paula-delrio-arteaga/FABACADEMY-1/Images/Lasercut.png

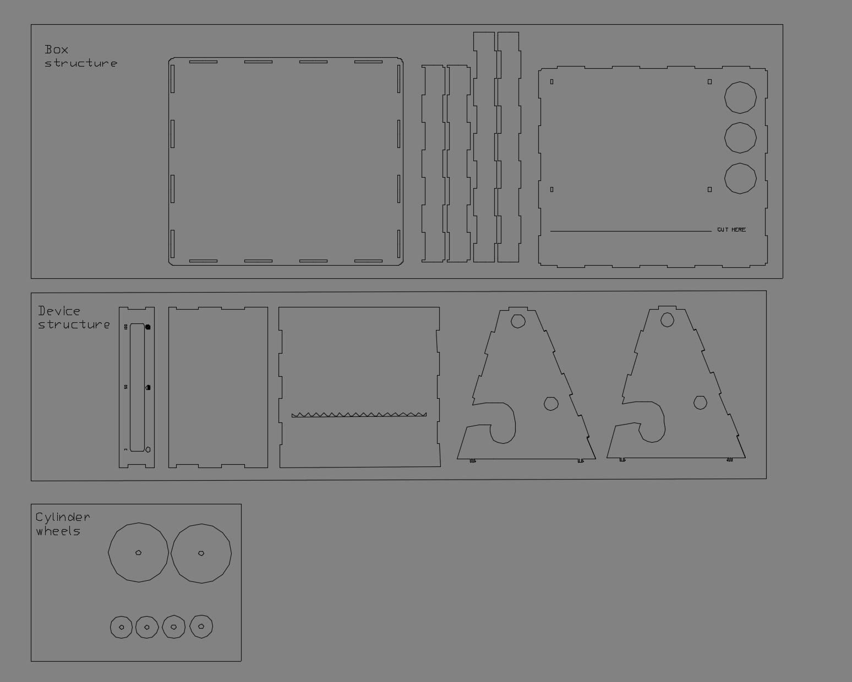
Images/Lasercut.png
