paula-delrio-arteaga/FABACADEMY-1/Images/prototyping_1.jpg

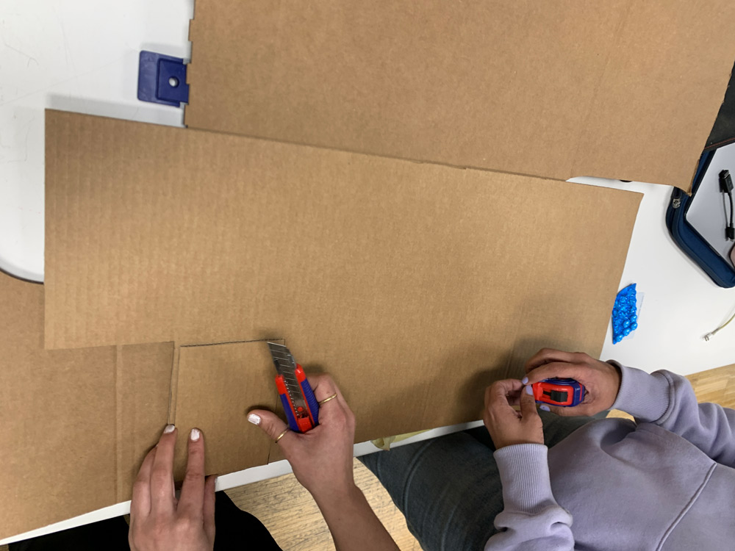
Images/prototyping_1.jpg
