paula-delrio-arteaga/FABACADEMY-1/Images/prototyping_2.jpg

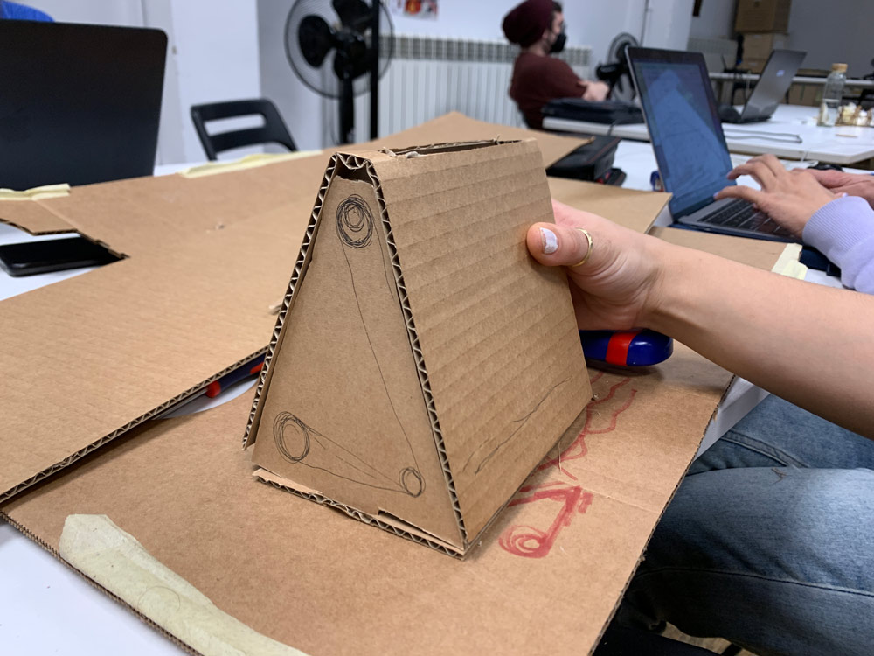
Images/prototyping_2.jpg
