paula-delrio-arteaga/FABACADEMY-1/Images/prototyping_3.jpg

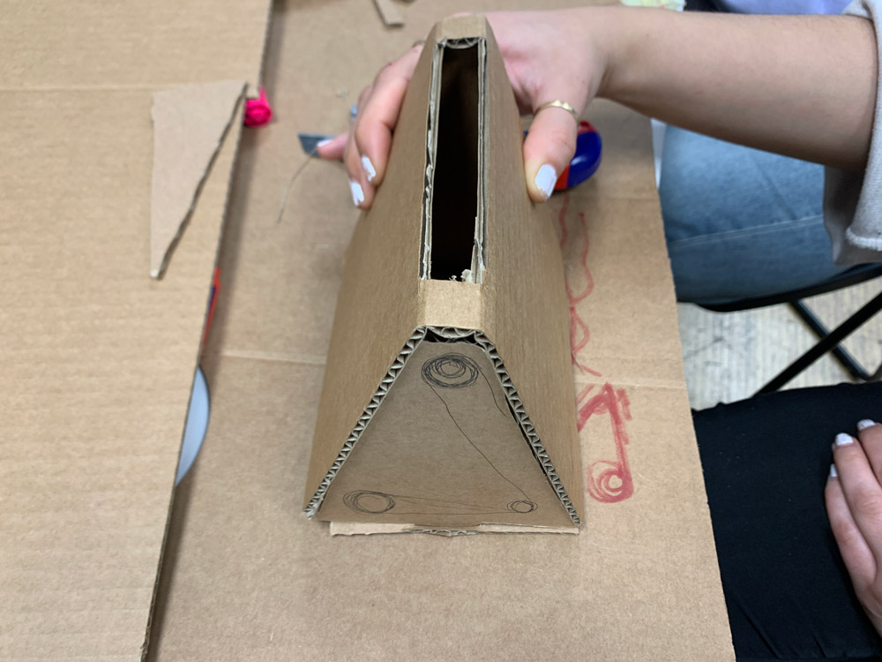
Images/prototyping_3.jpg
