paula-delrio-arteaga/FABACADEMY-1/Images/reference_01.jpg

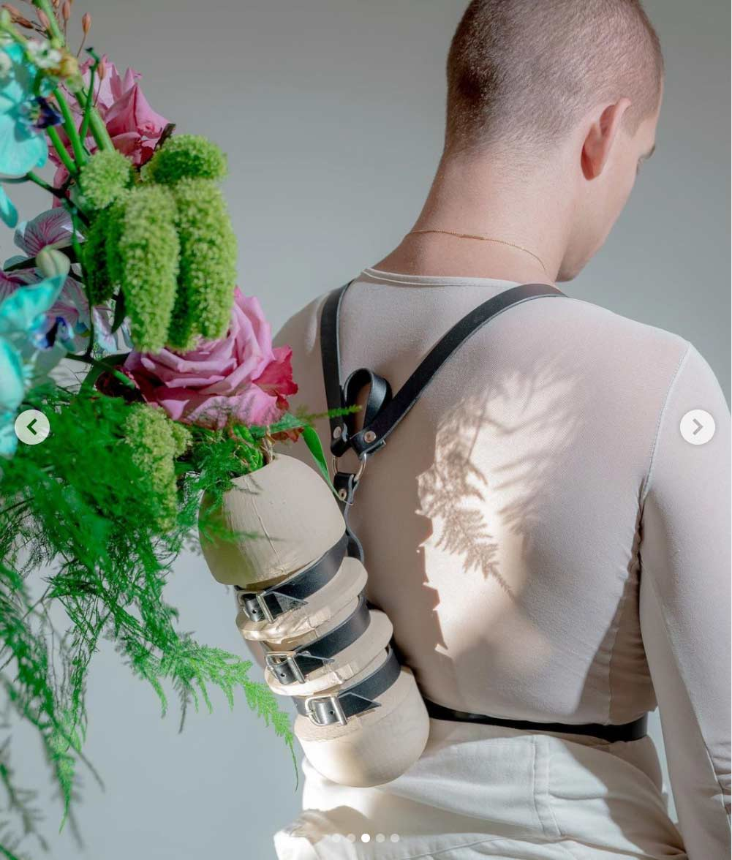
Images/reference_01.jpg
