paula-delrio-arteaga/FABACADEMY-1/Images/Reference_02.jpg

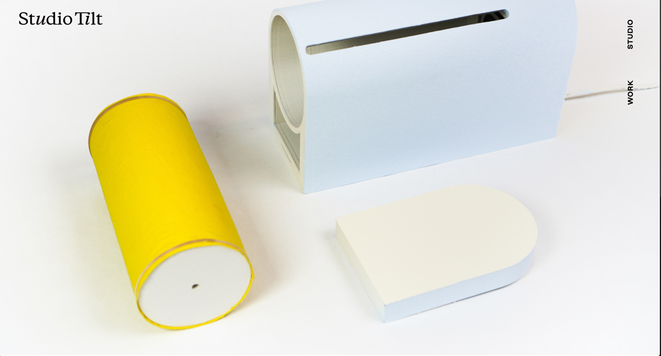
Images/Reference_02.jpg
