paula-delrio-arteaga/FABACADEMY-1/Images/sketch.png

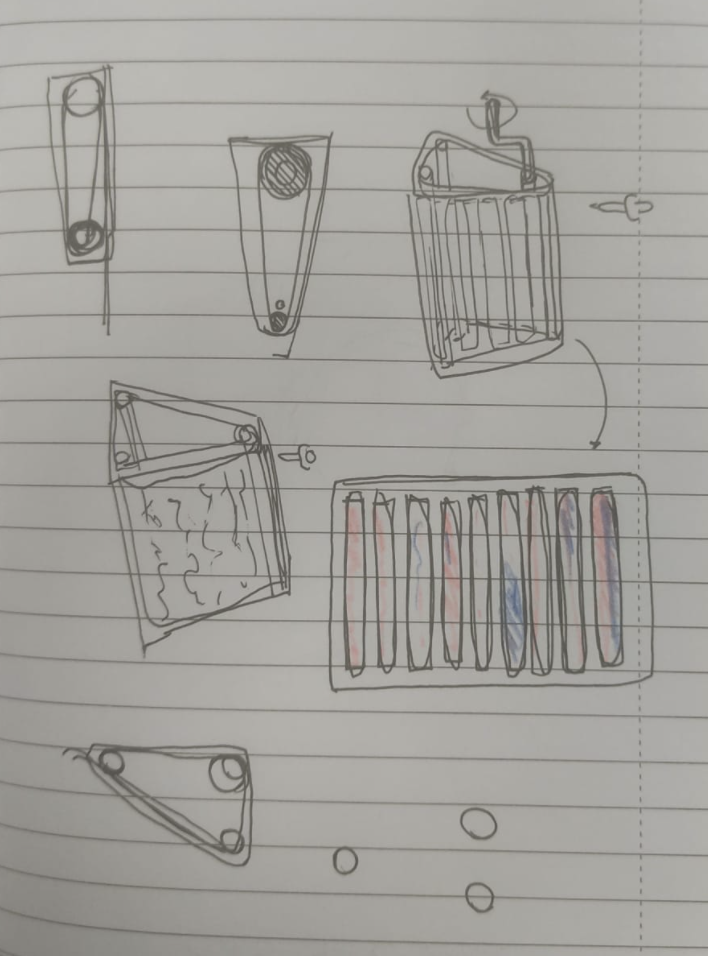
Images/sketch.png
